chaosloth/Connotron_DMX_Gateway/ESP32_ArtNet_DMX_Gateway/data/studio.png

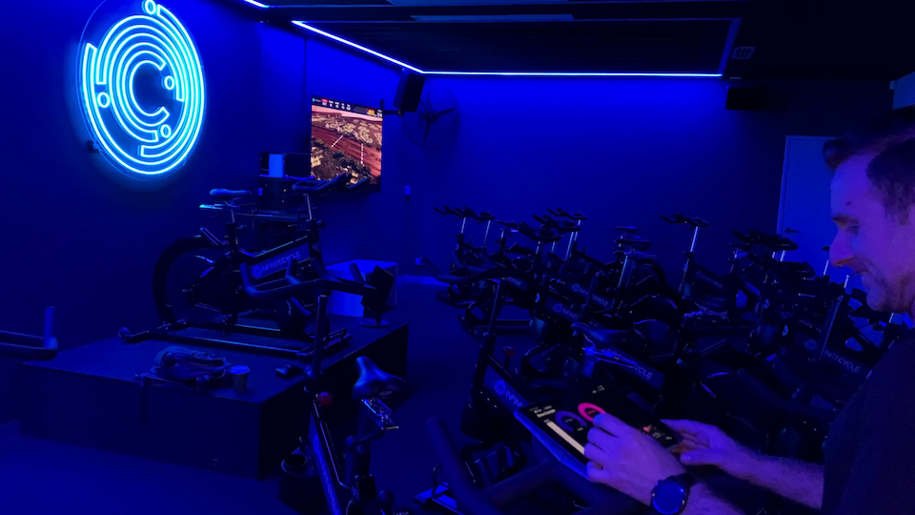
ESP32_ArtNet_DMX_Gateway/data/studio.png
